prototipado/verificador_imu/STLs/m5-nut-105 v2.stl

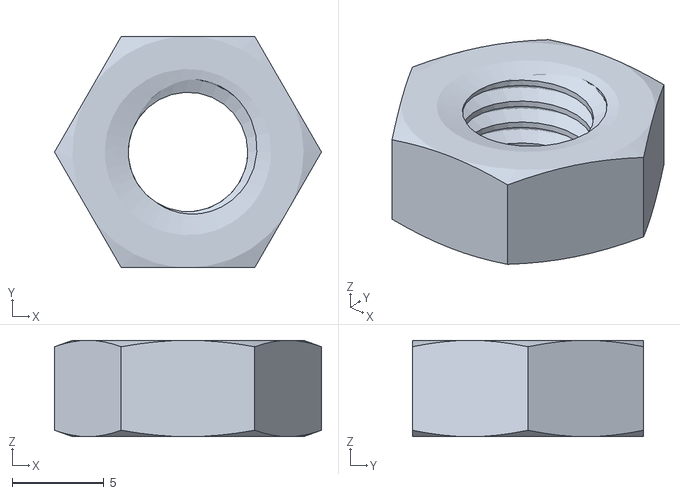
[picture p26: CAD file, 2024-09-06]
STLs/m5-nut-105 v2.stl
14.5 x 12.6 x 5.25
